eclipsevl/CH32V305-UAC2/HSDAC/User/codec.h

#pragma once

#include <stdint.h>
#include <stdbool.h>

bool Codec_Init();
void Codec_Handler();

void Codec_Start();
void Codec_Stop();

uint32_t Codec_GetSampleRate();
void     Codec_SetSampleRate(uint32_t sample_rate);

void    Codec_Mute(uint8_t channel, uint8_t mute);
uint8_t Codec_IsMute(uint8_t channel);
void    Codec_SetVolume(uint8_t channel, int16_t volume);
int16_t Codec_GetVolume(uint8_t channel);

uint32_t Codec_GetFeedbackFs();
