eclipsevl/CH32V305-UAC2/HSDAC/User/usb/tpusb/midiv2.hpp

#pragma once

// --------------------------------------------------------------------------------
// USB MIDI 2.0  https://usb.org/sites/default/files/USB%20MIDI%20v2_0.pdf
// --------------------------------------------------------------------------------

namespace tpusb::midiv2 {

}
